LeonSchober/rp2350A_fpga_board/hardware/3d/20260630_214651_1.jpg

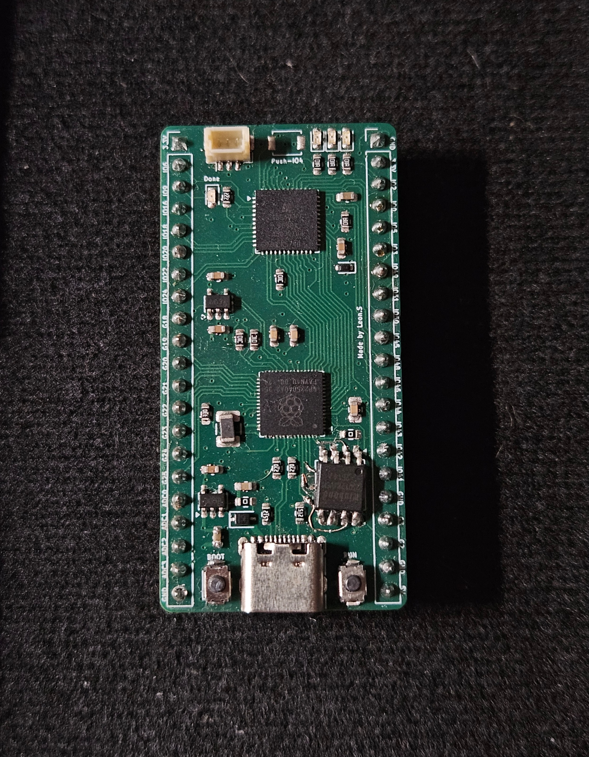
hardware/3d/20260630_214651_1.jpg
